duy-collab/Ivy_PetRobot/Ivy_Pics/2.jpg

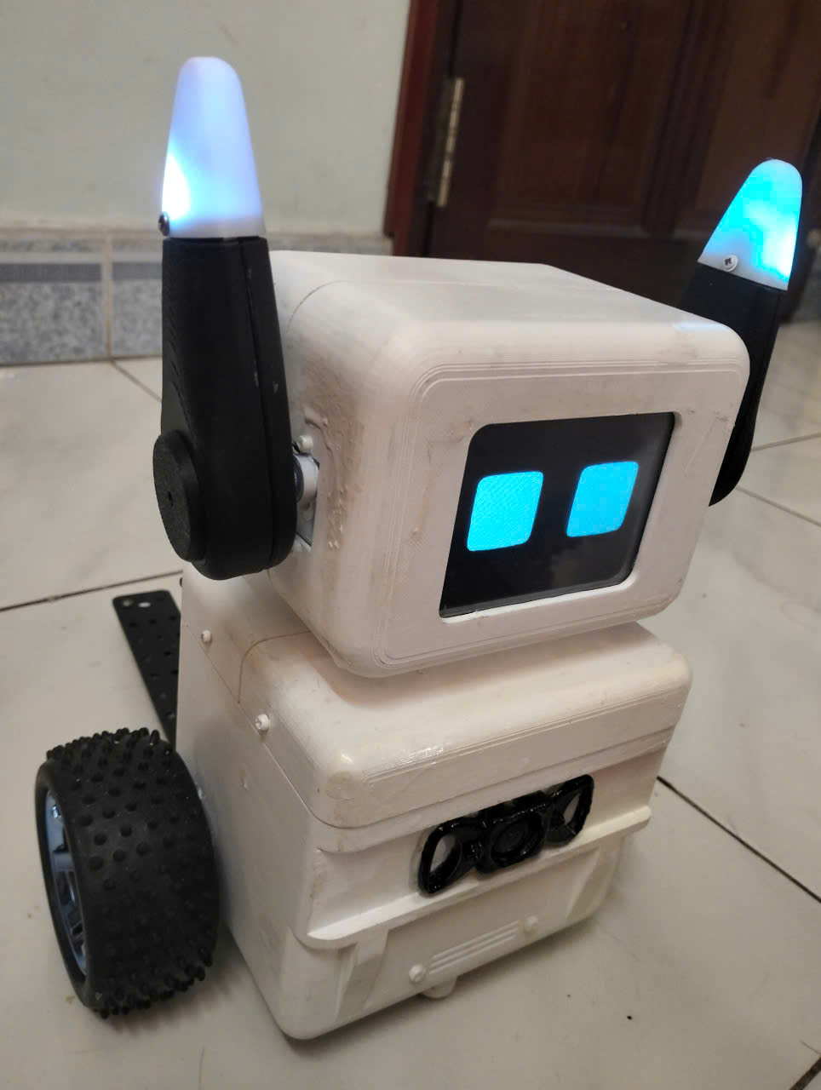
Ivy_Pics/2.jpg
