duy-collab/Ivy_PetRobot/Ivy_Pics/3.jpg

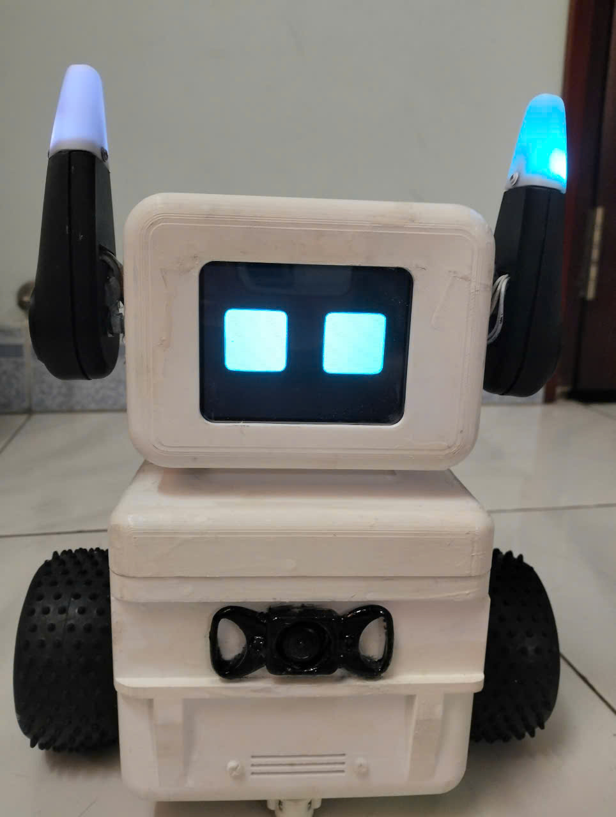
Ivy_Pics/3.jpg
