duy-collab/Ivy_PetRobot/Ivy_Pics/4.jpg

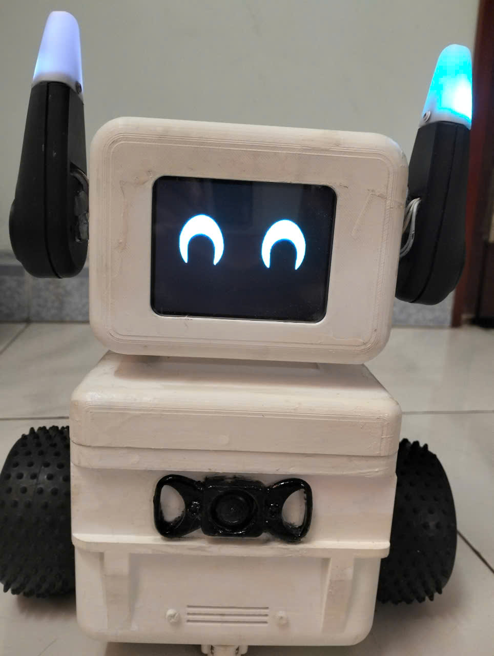
Ivy_Pics/4.jpg
