duy-collab/Ivy_PetRobot/Ivy_PRINT_3D/camera_OV5647_mount.STL

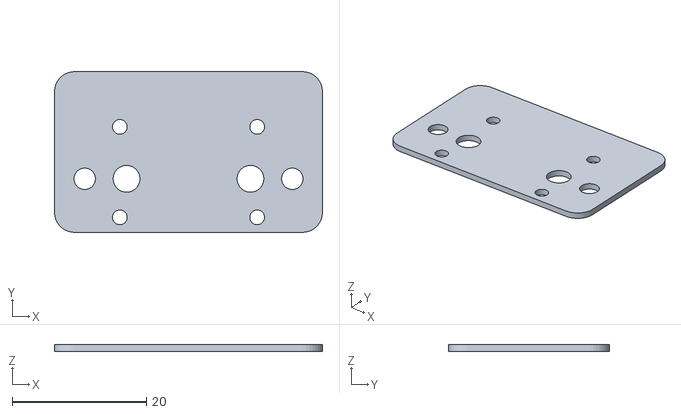
[picture p20: CAD file, 2025-05-10]
Ivy_PRINT_3D/camera_OV5647_mount.STL
40.0 x 24.0 x 1.00
