duy-collab/Ivy_PetRobot/Ivy_SolidWorks/HEAD/EAR/Top_Ear.SLDPRT

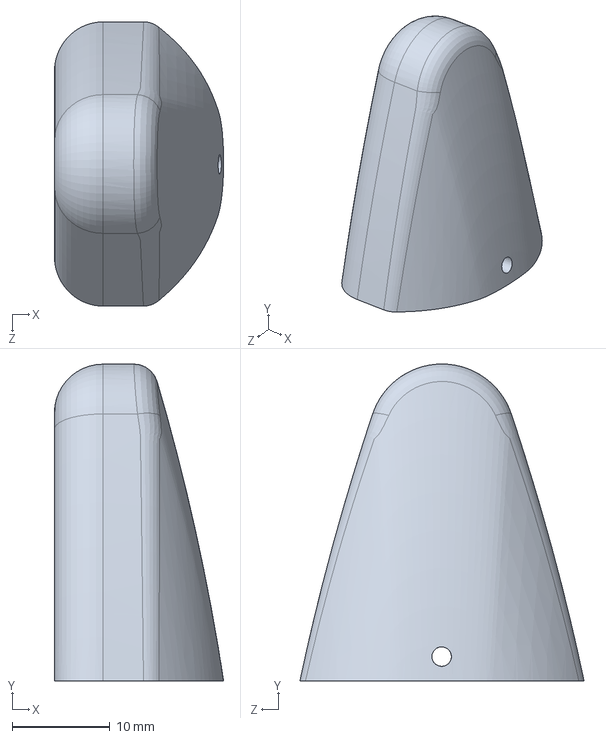
[picture p21: CAD file, 2025-05-10]
Ivy_SolidWorks/HEAD/EAR/Top_Ear.SLDPRT
17.4 x 32.5 x 29.1 mm
