duy-collab/Ivy_PetRobot/Ivy_SolidWorks/HEAD/PinHeader_1x03_P2.54mm_Horizontal.SLDPRT

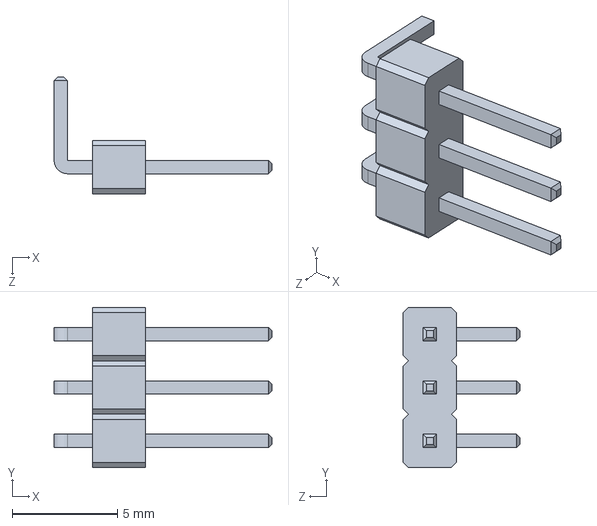
[picture p22: CAD file, 2025-05-10]
Ivy_SolidWorks/HEAD/PinHeader_1x03_P2.54mm_Horizontal.SLDPRT
10.4 x 7.62 x 5.54 mm
