duy-collab/Ivy_PetRobot/Ivy_SolidWorks/WHEEL/SHAFT COUPLER, JGB37-520.SLDPRT

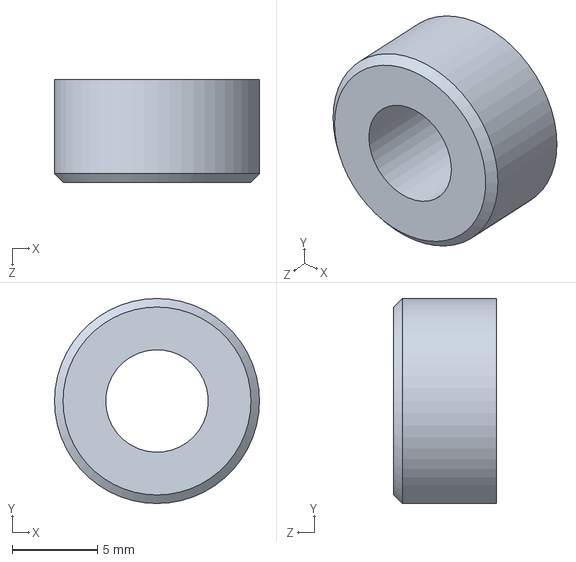
[picture p23: CAD file, 2025-05-10]
Ivy_SolidWorks/WHEEL/SHAFT COUPLER, JGB37-520.SLDPRT
12.0 x 12.0 x 6.00 mm
