duy-collab/Ivy_PetRobot/Ivy_SolidWorks/BODY/camera_OV5647.SLDPRT

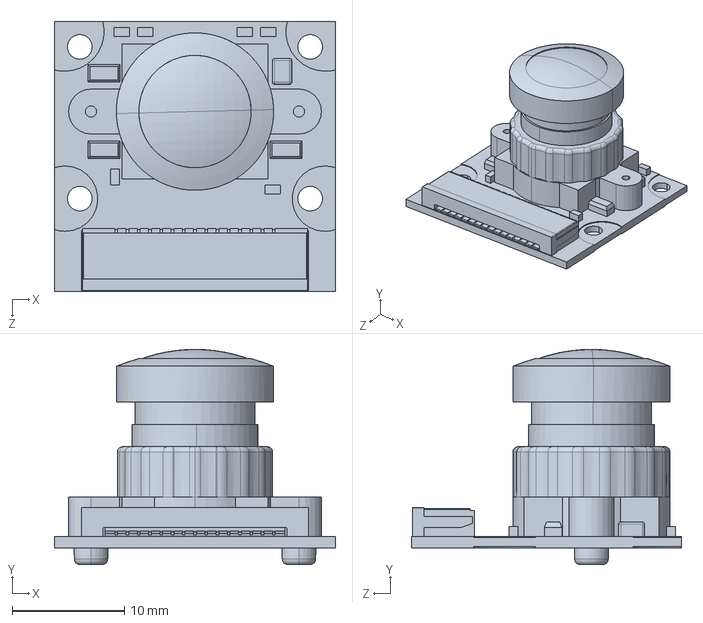
[picture p24: CAD file, 2025-05-10]
Ivy_SolidWorks/BODY/camera_OV5647.SLDPRT
25.0 x 19.2 x 24.0 mm
