duy-collab/Ivy_PetRobot/Ivy_SolidWorks/HEAD/EAR/new_mic_cover.SLDPRT

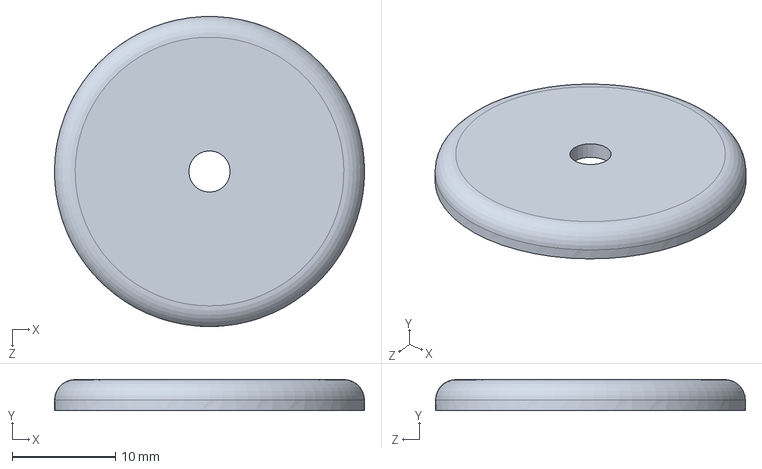
[picture p25: CAD file, 2025-05-10]
Ivy_SolidWorks/HEAD/EAR/new_mic_cover.SLDPRT
30.0 x 3.00 x 30.0 mm
