duy-collab/Ivy_PetRobot/Ivy_SolidWorks/HEAD/TFT_ILI9341_3.2inch.SLDPRT

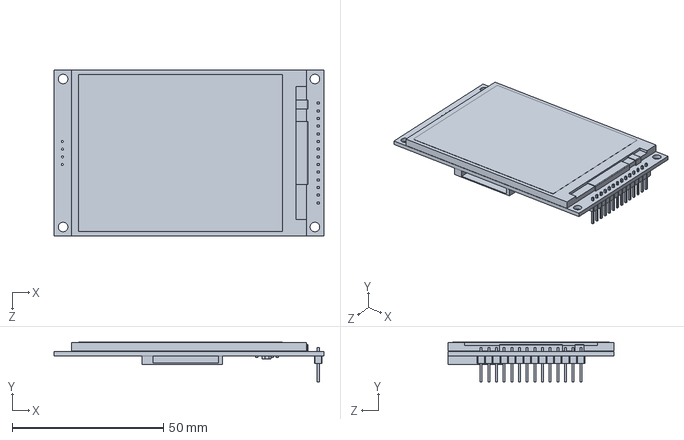
[picture p26: CAD file, 2025-05-10]
Ivy_SolidWorks/HEAD/TFT_ILI9341_3.2inch.SLDPRT
89.4 x 13.1 x 55.1 mm
