duy-collab/Ivy_PetRobot/Ivy_SolidWorks/WHEEL/PLASTIC COVER, DC MOTOR, JGB37-520.SLDPRT

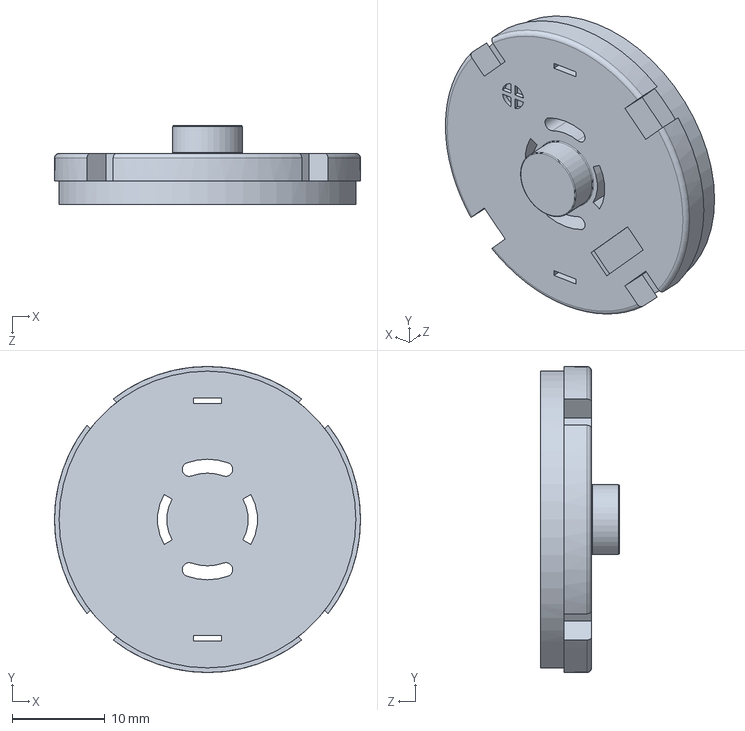
[picture p27: CAD file, 2025-05-10]
Ivy_SolidWorks/WHEEL/PLASTIC COVER, DC MOTOR, JGB37-520.SLDPRT
33.0 x 33.0 x 8.50 mm
