duy-collab/Ivy_PetRobot/Ivy_SolidWorks/BODY/bowtie.SLDPRT

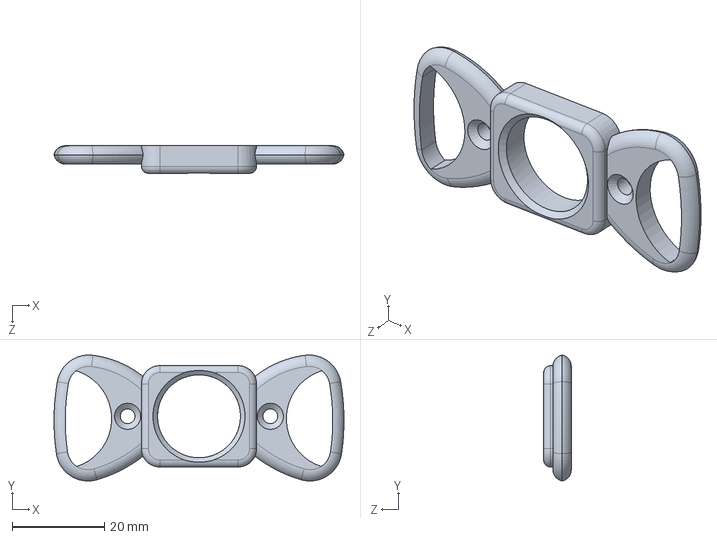
[picture p28: CAD file, 2025-05-10]
Ivy_SolidWorks/BODY/bowtie.SLDPRT
62.9 x 27.3 x 6.00 mm
