duy-collab/Ivy_PetRobot/Ivy_SolidWorks/HEAD/EAR/ear_mica_holder.SLDPRT

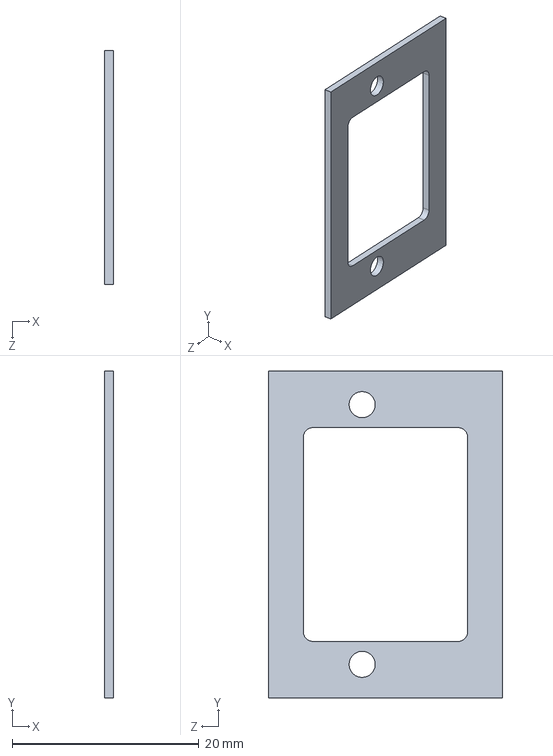
[picture p29: CAD file, 2025-05-10]
Ivy_SolidWorks/HEAD/EAR/ear_mica_holder.SLDPRT
1.00 x 35.0 x 25.0 mm
