duy-collab/Ivy_PetRobot/Ivy_SolidWorks/HEAD/TTP223B.SLDPRT

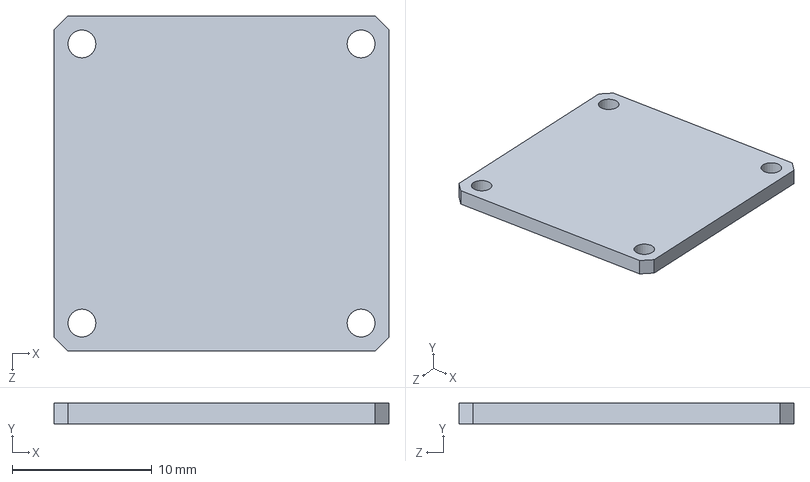
[picture p30: CAD file, 2025-05-10]
Ivy_SolidWorks/HEAD/TTP223B.SLDPRT
24.0 x 1.50 x 24.0 mm
