duy-collab/Ivy_PetRobot/Ivy_SolidWorks/WHEEL/wheel_adapter.SLDPRT

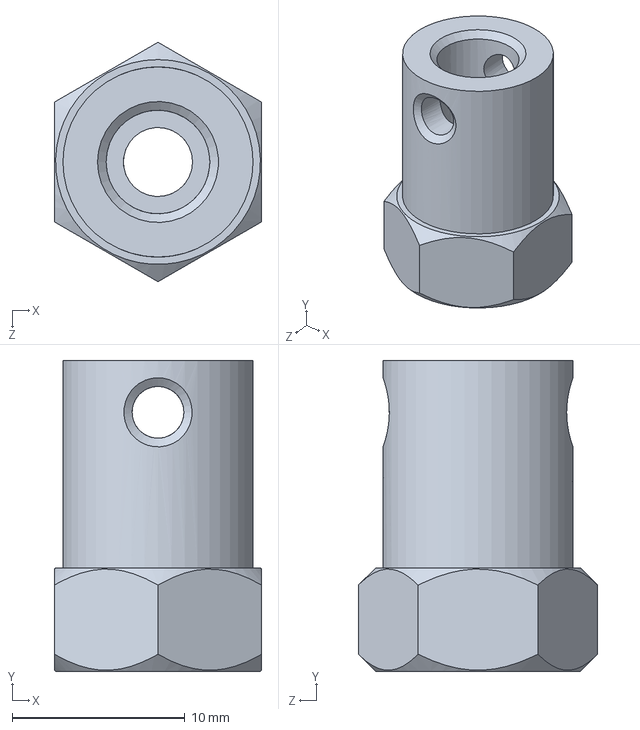
[picture p31: CAD file, 2025-05-10]
Ivy_SolidWorks/WHEEL/wheel_adapter.SLDPRT
12.0 x 18.0 x 13.9 mm
