duy-collab/Ivy_PetRobot/Ivy_PRINT_3D/TAI_TRONG.STL

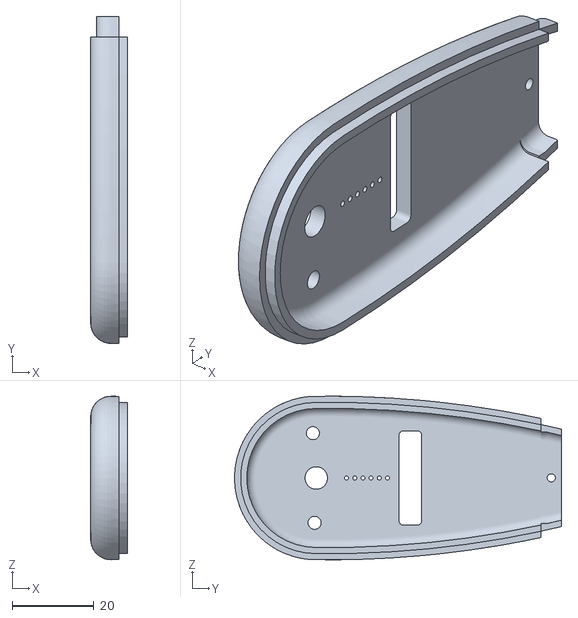
[picture p32: CAD file, 2025-05-10]
Ivy_PRINT_3D/TAI_TRONG.STL
9.00 x 80.0 x 40.0
