duy-collab/Ivy_PetRobot/Ivy_SolidWorks/BODY/caster_ball.SLDPRT

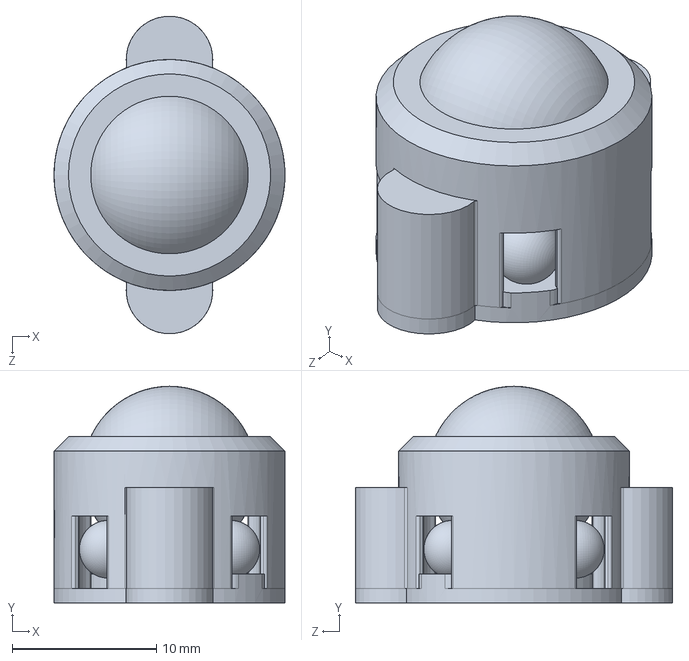
[picture p33: CAD file, 2025-05-10]
Ivy_SolidWorks/BODY/caster_ball.SLDPRT
16.0 x 15.0 x 22.0 mm
