duy-collab/Ivy_PetRobot/Ivy_SolidWorks/HEAD/SG90.SLDPRT

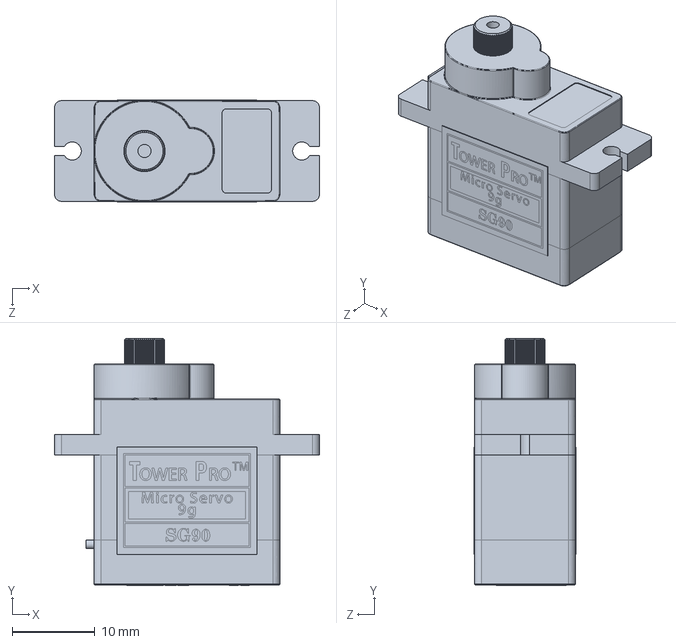
[picture p34: CAD file, 2025-05-10]
Ivy_SolidWorks/HEAD/SG90.SLDPRT
32.1 x 30.0 x 12.4 mm
