duy-collab/Ivy_PetRobot/Ivy_SolidWorks/WHEEL/85mm_Wheel.SLDPRT

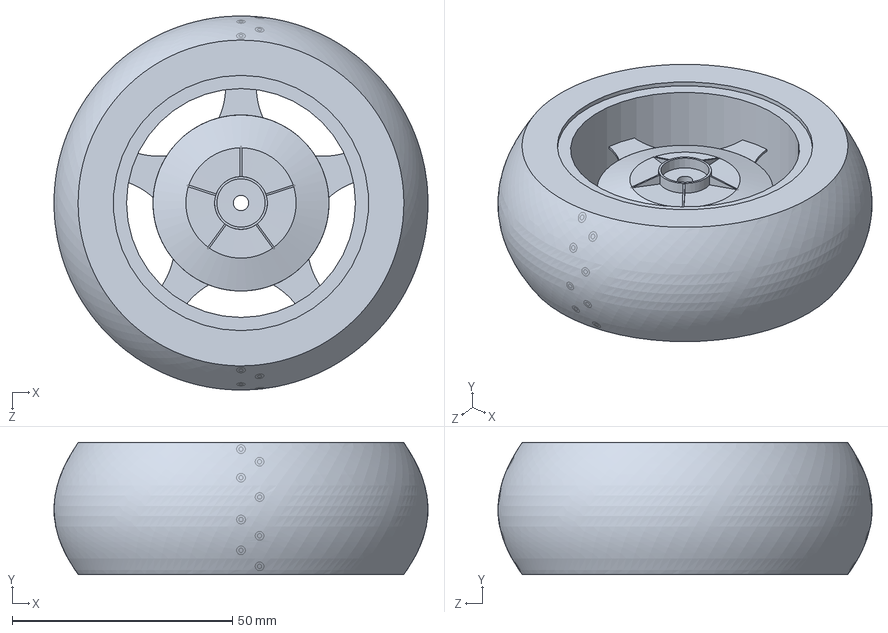
[picture p35: CAD file, 2025-05-10]
Ivy_SolidWorks/WHEEL/85mm_Wheel.SLDPRT
85.0 x 30.0 x 85.0 mm
