duy-collab/Ivy_PetRobot/Ivy_PRINT_3D/FrontHead.STL

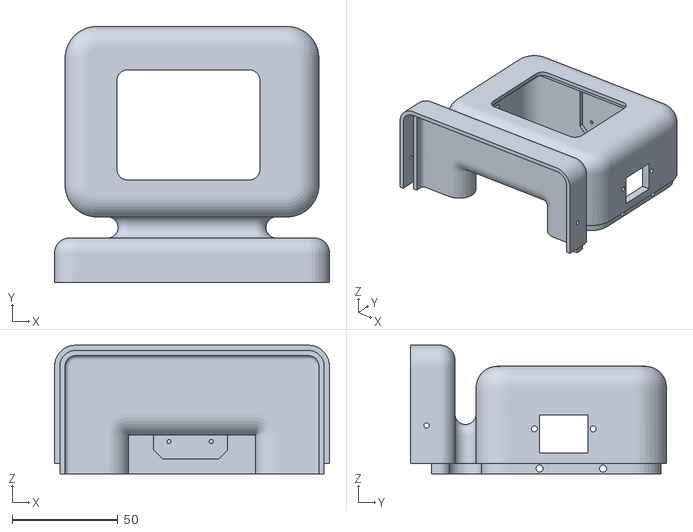
[picture p36: CAD file, 2025-05-10]
Ivy_PRINT_3D/FrontHead.STL
130.0 x 121.0 x 60.9
