duy-collab/Ivy_PetRobot/Ivy_SolidWorks/BODY/L298N.SLDPRT

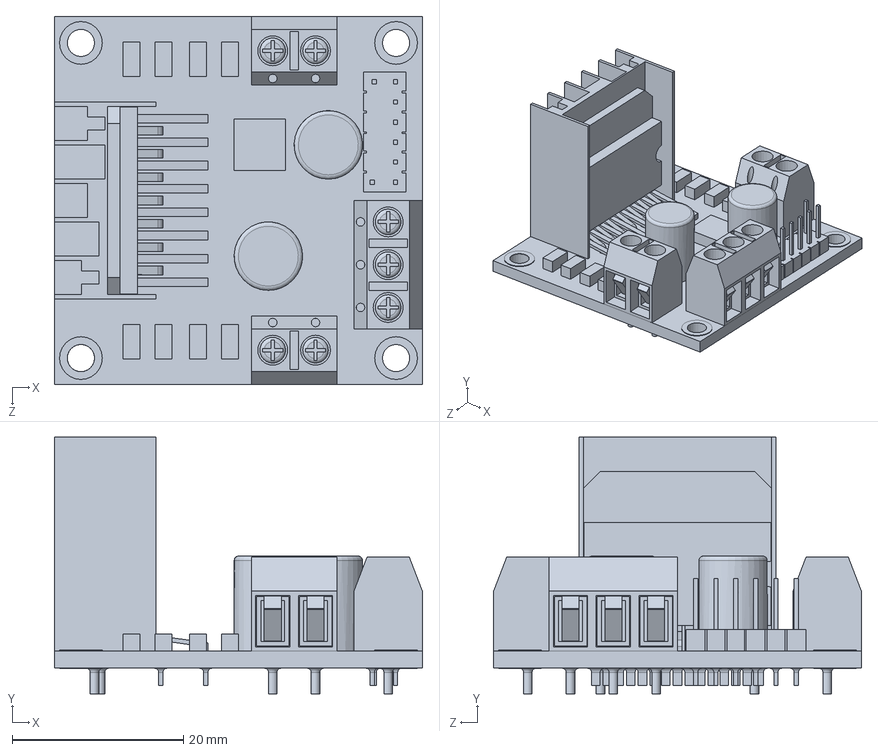
[picture p37: CAD file, 2025-05-10]
Ivy_SolidWorks/BODY/L298N.SLDPRT
43.0 x 30.0 x 43.0 mm
