duy-collab/Ivy_PetRobot/Ivy_SolidWorks/BODY/charging_port_5.5_2.1_DC.SLDPRT

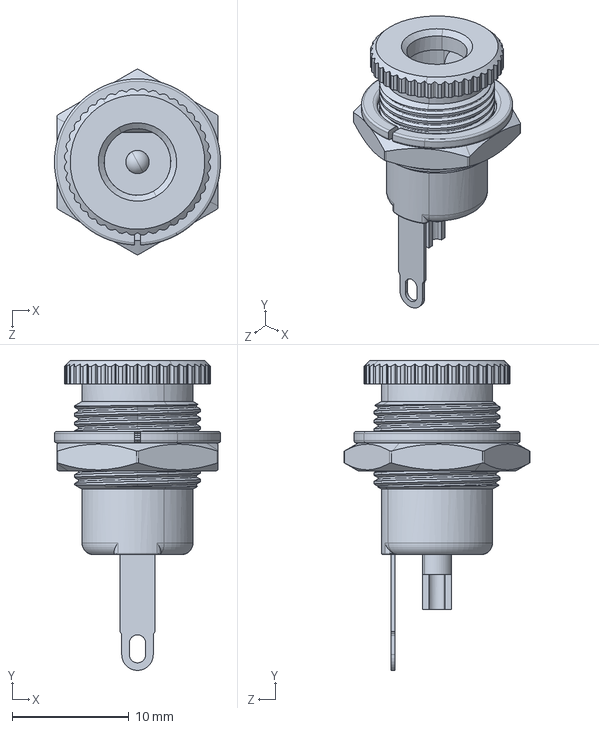
[picture p38: CAD file, 2025-05-10]
Ivy_SolidWorks/BODY/charging_port_5.5_2.1_DC.SLDPRT
14.2 x 26.5 x 15.9 mm
