duy-collab/Ivy_PetRobot/Ivy_SolidWorks/HEAD/EAR/spacer_10mm.SLDPRT

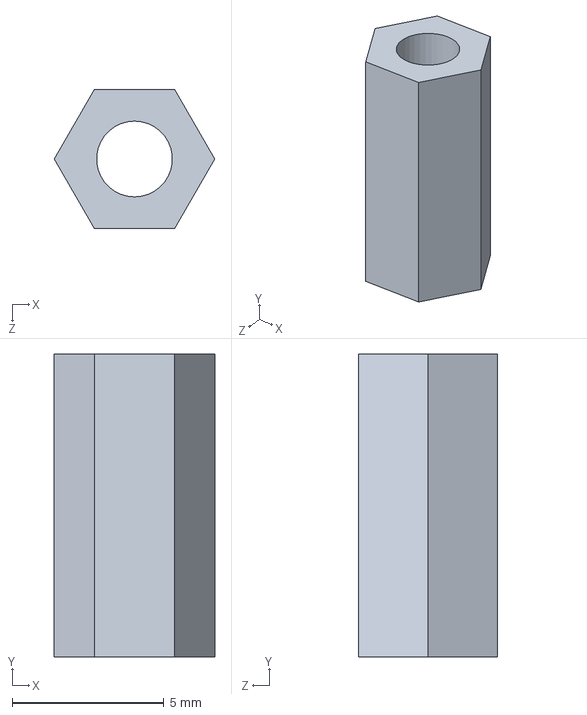
[picture p39: CAD file, 2025-05-10]
Ivy_SolidWorks/HEAD/EAR/spacer_10mm.SLDPRT
5.30 x 10.0 x 4.59 mm
