duy-collab/Ivy_PetRobot/Ivy_SolidWorks/HEAD/EAR/sg90_horn.SLDPRT

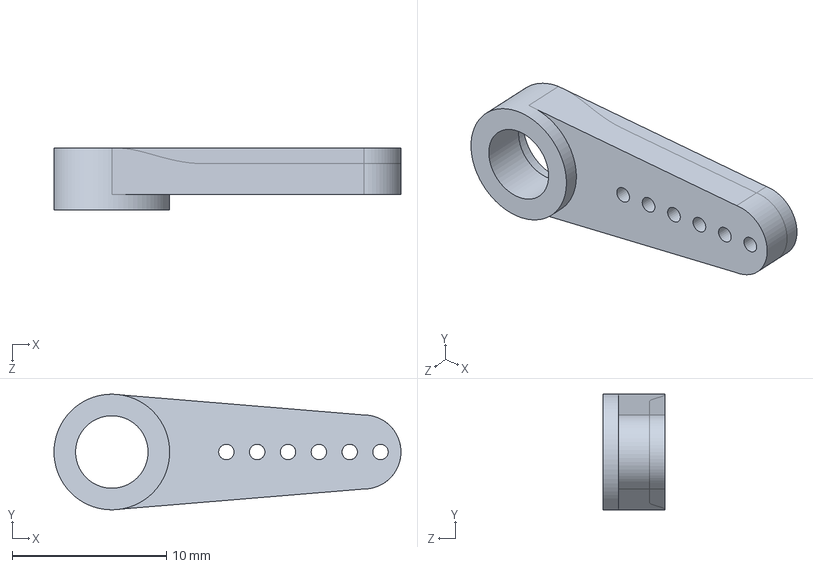
[picture p40: CAD file, 2025-05-10]
Ivy_SolidWorks/HEAD/EAR/sg90_horn.SLDPRT
22.5 x 7.50 x 4.00 mm
