duy-collab/Ivy_PetRobot/Ivy_SolidWorks/WHEEL/CONNECTION, DC MOTOR, JGB37-520.SLDPRT

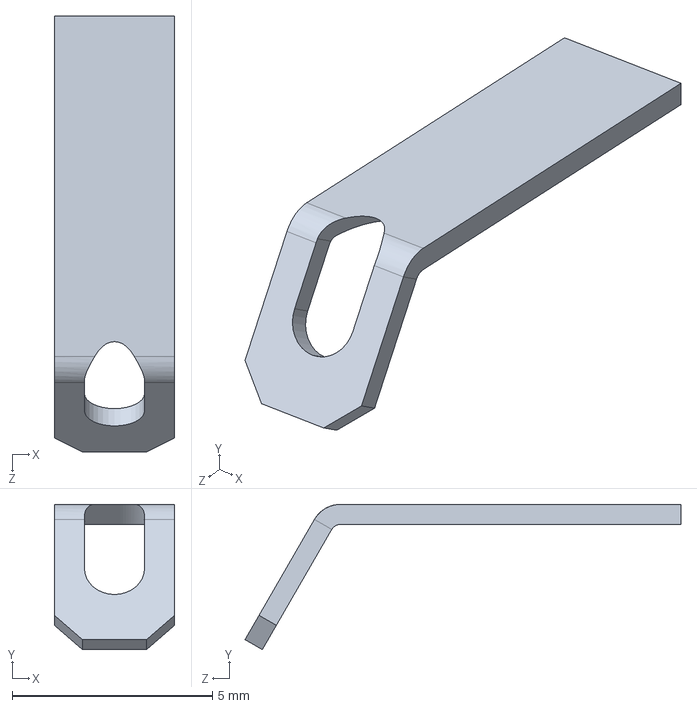
[picture p41: CAD file, 2025-05-10]
Ivy_SolidWorks/WHEEL/CONNECTION, DC MOTOR, JGB37-520.SLDPRT
3.00 x 3.62 x 10.9 mm
