duy-collab/Ivy_PetRobot/Ivy_SolidWorks/WHEEL/MOTOR SHAFT, JGB37-520.SLDPRT

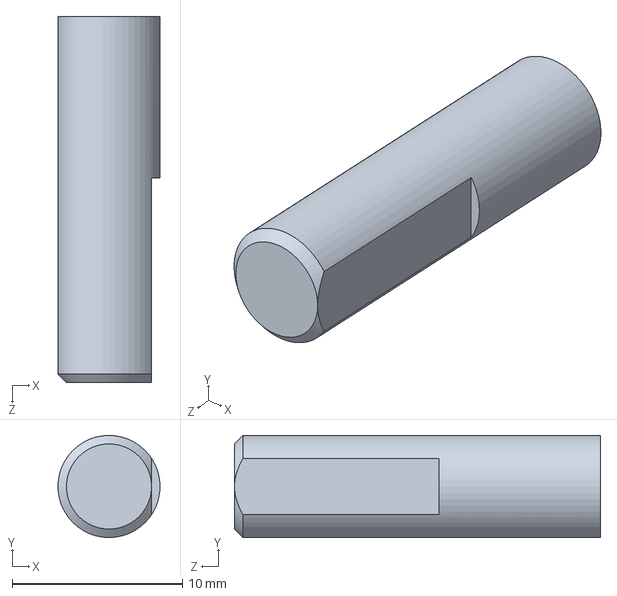
[picture p42: CAD file, 2025-05-10]
Ivy_SolidWorks/WHEEL/MOTOR SHAFT, JGB37-520.SLDPRT
6.00 x 6.00 x 21.5 mm
