duy-collab/Ivy_PetRobot/Ivy_SolidWorks/WHEEL/COUPLING BRACKET, GEARED BODY TO DC MOTOR, JGB37-520.SLDPRT

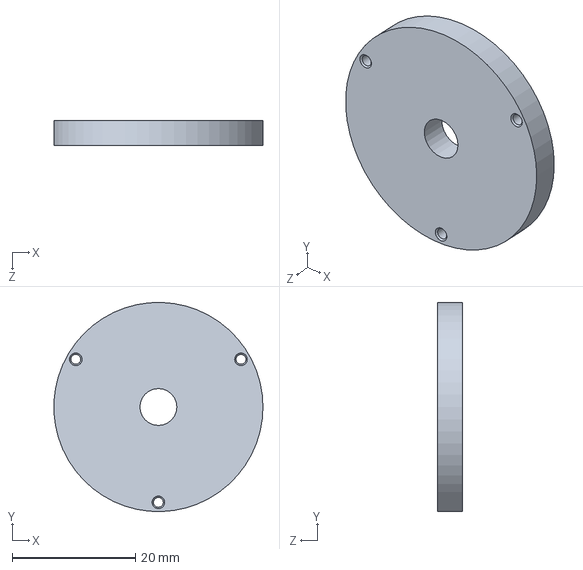
[picture p43: CAD file, 2025-05-10]
Ivy_SolidWorks/WHEEL/COUPLING BRACKET, GEARED BODY TO DC MOTOR, JGB37-520.SLDPRT
34.0 x 34.0 x 4.00 mm
